ahmedkelbanna91/2_my_Spacemouse/3D_Printable_Design_Files/knop cover.stl

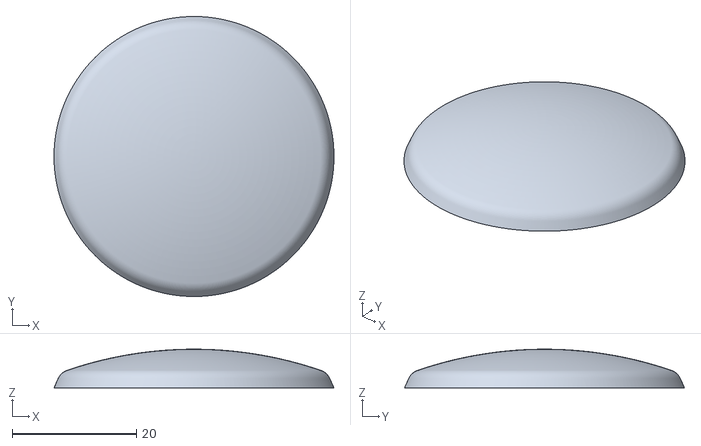
[picture p16: CAD file, 2025-07-08]
3D_Printable_Design_Files/knop cover.stl
45.1 x 45.1 x 6.22
