ahmedkelbanna91/2_my_Spacemouse/3D_Printable_Design_Files/esp32-fixer.stl

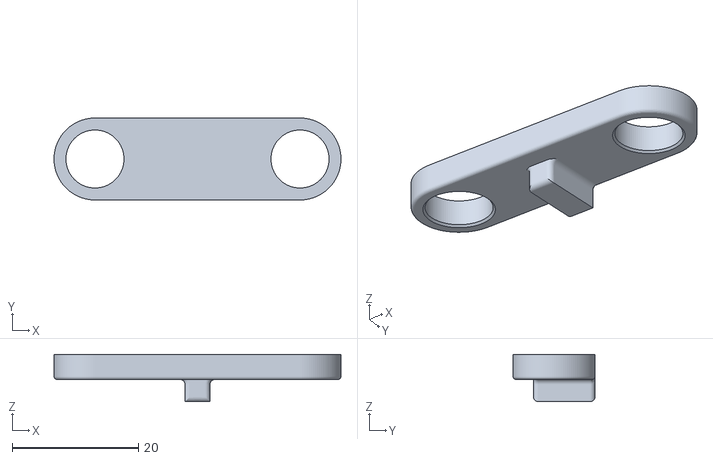
[picture p17: CAD file, 2025-07-08]
3D_Printable_Design_Files/esp32-fixer.stl
45.5 x 13.0 x 7.50
