ahmedkelbanna91/2_my_Spacemouse/calibration.h

// File for calibration specific functions
#include "config.h"


/// @brief Prints an array to the Serial, in order to copy the output again to C-Code. Example output: {-519, -521, -512, -2, -519, -482, -508, -1}
/// @param arr array to print
/// @param size size of the array
void printArray(int arr[], int size) {
  SERIAL.print("{");
  for (int i = 0; i < size; i++) {
    SERIAL.print(arr[i]);
    if (i < size - 1) {
      SERIAL.print(", ");
    }
  }
  SERIAL.println("}");
}


char const* axisNames[] = { "H0:", "H1:", "H2:", "H3:", "H5:", "H6:", "H7:", "H8:" };  // 8
char const* velNames[] = { "TX:", "TY:", "TZ:", "RX:", "RY:", "RZ:" };                 // 6

/// @brief Check, if a new debug output shall be generated. This is used in order to generate a debug line only every DEBUGDELAY ms, see config.h
/// @return true, if debug message is due
bool isDebugOutputDue() {
  static unsigned long lastDebugOutput = 0;  // time from millis(), when the last debug output was given
  if (millis() - lastDebugOutput > DEBUGDELAY) {
    lastDebugOutput = millis();
    return true;
  } else {
    return false;
  }
}

void debugOutput1(int* rawReads, int* keyVals) {
  if (isDebugOutputDue()) {
    // Report back raw ADC 10-bit values if enabled
    for (int i = 0; i < 8; i++) {
      SERIAL.printf("%2.2s: %4d  ", axisNames[i], rawReads[i]);
    }
#if NUMKEYS > 0
    SERIAL.print("\t");
#endif
    for (int i = 0; i < NUMKEYS; i++) {
      SERIAL.printf("K%d: %d  ", i, keyVals[i]);
    }
    SERIAL.print(DEBUG_LINE_END);
  }
}

void debugOutput2(int* centered, int* keyVals) {
  if (isDebugOutputDue()) {
    // this routine creates the output for the former debug = 2 and debug = 3
    for (int i = 0; i < 8; i++) {
      SERIAL.printf("%2.2s: %4d  ", axisNames[i], centered[i]);
    }
#if NUMKEYS > 0
    SERIAL.print("\t");
#endif
    for (int i = 0; i < NUMKEYS; i++) {
      SERIAL.printf("K%d: %d  ", i, keyVals[i]);
    }
    SERIAL.print(DEBUG_LINE_END);
  }
}

/// @brief Report translation and rotation values if enabled.
/// @param velocity pointer to velocity array
/// @param keyOut pointer to keyOut array
void debugOutput4(int16_t* velocity, uint8_t* keyOut) {
  //
  if (isDebugOutputDue()) {
    for (int i = 0; i < 6; i++) {
      SERIAL.printf("%2.2s: %4d  ", velNames[i], velocity[i]);
    }
#if NUMKEYS > 0
    SERIAL.print("\t");
#endif
    for (int i = 0; i < NUMKEYS; i++) {
      SERIAL.printf("K%d: %d  ", i, keyOut[i]);
    }
    SERIAL.print(DEBUG_LINE_END);
  }
}

/// @brief Report single axis and resulting velocities info side by side for direct reference. Very useful if you need to alter which inputs are used in the arithmetic above.
/// @param centered pointer to arrays of 8 axis
/// @param velocity pointer to array of 6 velocities
void debugOutput5(int* centered, int16_t* velocity) {
  if (isDebugOutputDue()) {
    for (int i = 0; i < 8; i++) {
      SERIAL.printf("%2.2s: %4d  ", axisNames[i], centered[i]);
    }
#if NUMKEYS > 0
    SERIAL.print("\t");
#endif
    for (int i = 0; i < 6; i++) {
      SERIAL.printf("%2.2s: %4d  ", velNames[i], velocity[i]);
    }
    SERIAL.print(DEBUG_LINE_END);
  }
}

// Variables and function to get the min and maximum value of the centered values
int minMaxCalcState = 0;  // little state machine -> setup in 0 -> measure in 1 -> output in 2 ->  end in 3
int minValue[8];          // Array to store the minimum values
int maxValue[8];          // Array to store the maximum values
unsigned long startTime;  // Start time for the measurement


/// @brief This function records the minimum and maximum movement of the joysticks: After initialization, move the mouse for 15s and see the printed output. Replug/reset the mouse, to enable the semi-automatic calibration for a second time.
/// @param centered pointer to the array with the centered joystick values
void calcMinMax(int* centered) {
  if (minMaxCalcState == 0) {
    delay(3000);
    // Initialize the arrays
    for (int i = 0; i < 8; i++) {
      minValue[i] = 1023;  // Set the min value to the maximum possible value
      maxValue[i] = 0;     // Set the max value to the minimum possible value
    }
    startTime = millis();  // Record the current time
    minMaxCalcState = 1;   // next State: measure!
    SERIAL.println(F("Please start moving the spacemouse around for 15 sec!"));
  } else if (minMaxCalcState == 1) {
    if (millis() - startTime < 15000) {
      for (int i = 0; i < 8; i++) {
        // Update the minimum and maximum values
        if (centered[i] < minValue[i]) {
          minValue[i] = centered[i];
        }
        if (centered[i] > maxValue[i]) {
          maxValue[i] = centered[i];
        }
      }
    } else {
      // 15s are over. go to next state and report via console
      SERIAL.println(F("\n\nStop moving the spacemouse. These are the result. Copy them in config.h"));
      minMaxCalcState = 2;
    }
  } else if (minMaxCalcState == 2) {
    SERIAL.print(F("#define MINVALS "));
    printArray(minValue, 8);
    SERIAL.print(F("#define MAXVALS "));
    printArray(maxValue, 8);

    // Calculate and print the ranges for each HALL sensor
    int minmaxRanges[8];
    int max = 0;
    int min = 0;
    for (uint8_t i = 0; i < 8; i++) {
      minmaxRanges[i] = abs(minValue[i]) + abs(maxValue[i]);
      max = (abs(maxValue[i]) > max) ? abs(maxValue[i]) : max;
      min = (abs(minValue[i]) > min) ? abs(minValue[i]) : min;
    }
    SERIAL.print(F("Ranges are: "));
    printArray(minmaxRanges, 8);
    int centerPoint = (max + (min * -1)) / 2;
    SERIAL.printf("Centerpoint: %d\n", centerPoint);

    for (int i = 0; i < 8; i++) {
      if (abs(minValue[i]) < MINMAX_MINWARNING) {
        SERIAL.printf("Warning: minValue[%d] %2.2s is small: %d\n", i, axisNames[i], minValue[i]);
      }
      if (abs(maxValue[i]) < MINMAX_MAXWARNING) {
        SERIAL.printf("Warning: maxValue[%d] %2.2s is small: %d\n", i, axisNames[i], maxValue[i]);
      }
    }
    minMaxCalcState = 3;  // no further reporting
  }
}

/// @brief Calibrate (=zero) the space mouse. The function is blocking other functions of the spacemouse during zeroing.
/// @param centerPoints
/// @param numIterations How many readings are taken to calculate the mean. Suggestion: 500 iterations, they take approx. 480ms.
/// @param debugFlag With debugFlag = true, a suggestion for the dead zone is given on the serial interface to save to the config.h
/// @return returns true, if no warnings occured. Warnings are given if the zero positions are very unlikely
bool busyZeroing(int* centerPoints, uint16_t numIterations, boolean debugFlag) {
  bool noWarningsOccured = true;
  if (debugFlag == true)
    SERIAL.println(F("\nZeroing HALL Sensors..."));

  int act[8];                                     // actual value
  uint32_t mean[8] = { 0, 0, 0, 0, 0, 0, 0, 0 };  // Array to count all values during the averaging
  int minValue[8];                                // Array to store the minimum values
  int maxValue[8];                                // Array to store the maximum values
  for (int i = 0; i < 8; i++) {
    minValue[i] = analogMax_Resolution;  // Set the min value to the maximum possible value
    maxValue[i] = 0;                     // Set the max value to the minimum possible value
  }

  // measure duration
  unsigned int long start, end;
  start = millis();

  uint16_t count;
  readAllFromSensors(act);
  for (count = 0; count < numIterations; count++) {
    readAllFromSensors(act);
    for (uint8_t i = 0; i < 8; i++) {
      // Add to mean
      mean[i] = mean[i] + act[i];
      // Update the minimum and maximum values for dead zone evaluation
      if (act[i] < minValue[i]) {
        minValue[i] = act[i];
      }
      if (act[i] > maxValue[i]) {
        maxValue[i] = act[i];
      }
    }
  }

  int16_t deadZone[8];
  int16_t maxDeadZone = 0;
  // calculating average by dividing the mean by the number of iterations
  for (uint8_t i = 0; i < 8; i++) {
    centerPoints[i] = mean[i] / count;
    deadZone[i] = maxValue[i] - minValue[i];
    if (deadZone[i] > maxDeadZone) {
      // get maximum deadzone independet of axis
      maxDeadZone = deadZone[i];
    }

    if (deadZone[i] > DEADZONEWARNING || centerPoints[i] < CENTERPOINTWARNINGMIN || centerPoints[i] > CENTERPOINTWARNINGMAX) {
      noWarningsOccured = false;
    }
  }

  // report everything, if with debugFlag
  if (debugFlag) {
    SERIAL.println(F("##  Min - Mean - Max -> Dead Zone"));
    for (int i = 0; i < 8; i++) {
      SERIAL.printf("%2.2s: %d - %d - %d - %d  ", axisNames[i], minValue[i], centerPoints[i], maxValue[i], deadZone[i]);
      if (deadZone[i] > DEADZONEWARNING) {
        SERIAL.print(F(" Attention! Moved axis?"));
      }
      if (centerPoints[i] < CENTERPOINTWARNINGMIN || centerPoints[i] > CENTERPOINTWARNINGMAX) {
        SERIAL.print(F(" Attention! Axis in idle?"));
      }
      SERIAL.println();
    }
    end = millis();
    SERIAL.println(F("Using mean as zero position..."));
    SERIAL.print(F("Suggestion for config.h: "));
    SERIAL.print(F("#define DEADZONE "));
    SERIAL.println(maxDeadZone);
    SERIAL.print(F("This took "));
    SERIAL.print(end - start);
    SERIAL.print(F(" ms for "));
    SERIAL.print(count);
    SERIAL.println(F(" iterations.\n"));
  }
  return noWarningsOccured;
}

uint16_t iterationsPerSecond = 0;       // count the iterations within one second
unsigned long lastFrequencyUpdate = 0;  // time from millis(), when the last frequency was calculated

/// @brief update and report the function to learn at what frequency the loop is running
void updateFrequencyReport() {
  // increase iterations counter
  iterationsPerSecond++;
  if (millis() - lastFrequencyUpdate > 1000) {  // if one second has past: report frequency
    SERIAL.print("Frequency: ");
    SERIAL.print(iterationsPerSecond);
    SERIAL.println(" Hz");
    lastFrequencyUpdate = millis();  // reset timer
    iterationsPerSecond = 0;         // reset iteration counter
  }
}


void checkCalibrationCMD(bool LED_, int16_t* velocity) {
  static bool lastLEDState = false;
  static uint8_t BlinkCount = 0;
  static unsigned long firstBlinkTime = 0;
  static unsigned long last_led_state_delay = 0;
  static bool timerRunning = false;
  static bool commandSent = false;

  if (millis() - last_led_state_delay > 10) {
    if (LED_ != lastLEDState) {
      lastLEDState = LED_;

      if (!timerRunning) {
        timerRunning = true;
        firstBlinkTime = millis();
        BlinkCount = 1;
        commandSent = false;
      } else if (!commandSent) {
        BlinkCount++;
      }
    }

    if (timerRunning && (millis() - firstBlinkTime > LED_BLINKING_COUNT_CALIBRATION_DELAY)) {
      BlinkCount = 0;
      timerRunning = false;
      commandSent = false;
    }
    last_led_state_delay = millis();

    if (timerRunning && BlinkCount >= 14 && !commandSent) {
#ifdef LEDpin
      showled(0, 0, MaxLEDbrightness);
#endif
      sendToSpaceMouse("q00");
      sendToSpaceMouse("n?");
      sendToSpaceMouse("z");
      // sendToSpaceMouse("m0");
      snprintf(lastMessage, sizeof(lastMessage), "Calibrating");
      lastMessageCompleted = false;
      commandSent = true;
      BlinkCount = 0;
      timerRunning = false;
      return;
    }

    if (timerRunning && BlinkCount >= 4 && !commandSent) {
      showled(0, 0, MaxLEDbrightness);
    } else {
      if (isSleeping) {
        fade(true, true, 10, MaxLEDbrightness - 100, 1, 10, false);
      } else {
        updateLEDsBasedOnMotion(LED_);
        updateLEDsBasedOnMotion(velocity, LED_);
      }
    }
    //     DPRINT(F("LEDstate: "));
    //     DPRINT(LED_);
    //     DPRINT(F("      BlinkCount: "));
    //     DPRINTLN(BlinkCount);
  }
}

// void autoCalibrateAndSleep() {
//   static unsigned long lastActivityTime = 0;
//   static bool isCalibrated = false;

//   bool activity = transData[0] != 0 || transData[1] != 0 || transData[2] != 0 || rotData[0] != 0 || rotData[1] != 0 || rotData[2] != 0 || buttonsData != 0;

//   if (activity) {
//     lastActivityTime = millis();
//     if (isSleeping) {
//       isSleeping = false;
//       snprintf(lastMessage, sizeof(lastMessage), "Waking up...");
//       // lastMessageCompleted = false;
//     }
//     isCalibrated = false;
//     return;
//   }

//   unsigned long idleTime = millis() - lastActivityTime;

//   // First level: Auto-calibration
//   if (!isCalibrated && idleTime > CALIBRATION_TIMEOUT) {
//     showled(0, 0, MaxLEDbrightness);
//     sendToSpaceMouse("q00");
//     sendToSpaceMouse("n?");
//     sendToSpaceMouse("z");
//     snprintf(lastMessage, sizeof(lastMessage), "Calibrating");
//     lastMessageCompleted = false;
//     isCalibrated = true;
//   }

//   if (!isSleeping && idleTime > SLEEP_TIMEOUT) {
//     // sendToSpaceMouse("m0");
//     snprintf(lastMessage, sizeof(lastMessage), "Sleeping...");
//     snprintf(modeLabel, sizeof(modeLabel), "%s", lastMessage);
//     isSleeping = true;

//     DPRINTLN("Entering Sleep Mode.");
//   }
// }
